arjunmehtaa/motion-capture-lite/tag_wifi.ino

#include <ESP8266WiFi.h>
#include <WiFiUdp.h>

const int NUM_LEDS = 4;
const int NUM_SEQUENCES = 5;
int ledArr[NUM_LEDS];

/* Assign pins */
const int ANALOG_PIN = A0;

/* Setup WiFi paramteres */
const char* ssid     = "dlink-A40C";
const char* password = "qybmo02053";
IPAddress local_ip(192, 168, 0, 13);                                                             
IPAddress gateway(192, 168, 0, 1);
IPAddress subnet(255, 255, 255, 0);

WiFiUDP Udp;
const char* host = "192.168.75.154";
unsigned int portToListen = 4210;  // local port to listen on
unsigned int portToSend = 5000;
char incomingPacket[2];  // buffer for incoming packets
char replyPacket[100];
unsigned long timeWindow = 10;
unsigned long readingWindow = 4;
unsigned long delayStartTime;
unsigned long delayEndTime;
unsigned long timeDelay = (timeWindow - readingWindow) / 2;
unsigned long startTime;
unsigned long currentTime;
unsigned long sequenceNumber;
bool startReading = false;
int inputVoltage = 0;

void setup() {
  Serial.begin(19200);
  pinMode(0, OUTPUT);

  // turn LED ON by default
  digitalWrite(0, LOW);
  sequenceNumber = 0;

  // We start by connecting to a WiFi network

  Serial.printf("Time window: %u, Reading window: %u\n", timeWindow, readingWindow);
  Serial.print("Connecting to ");
  Serial.println(ssid);
  
  
  WiFi.config(local_ip, gateway, subnet);
  WiFi.begin(ssid, password);
  
  while (WiFi.status() != WL_CONNECTED) {
    delay(500);
    Serial.print(".");
  }

  Serial.println("");
  Serial.println("WiFi connected");  
  // turn LED OFF when WiFi is connected
  digitalWrite(0, HIGH);
  Serial.println("IP address: ");
  Serial.println(WiFi.localIP());
  uint16 ab = Udp.begin(portToListen);
  Serial.printf("Now listening at IP %s, UDP port %d, %d\n", WiFi.localIP().toString().c_str(), portToListen, ab);

  memset(ledArr, 0, sizeof(ledArr));
}

int value = -1;

void loop() {
  currentTime = millis();
  int packetSize = Udp.parsePacket();
  if (packetSize) {

    int len = Udp.read(incomingPacket, 2);
    if (len > 0) {
      incomingPacket[len] = 0;
    }
    sequenceNumber = atoi(&incomingPacket[0]);
    // Serial.println(sequenceNumber);

    // receive incoming UDP packets
    value = 0;
    // Serial.println("Received");
    // Serial.printf("Received %d bytes from %s, port %d\n", packetSize, Udp.remoteIP().toString().c_str(), Udp.remotePort());
    startReading = true;
    startTime = currentTime;
    delayStartTime = startTime + timeDelay;
    delayEndTime = startTime + timeWindow - timeDelay;
  }
  if(startReading) {
    if(currentTime >= delayStartTime && currentTime <= delayEndTime) {
      inputVoltage = max(inputVoltage, analogRead(ANALOG_PIN)); 
    }
    if (currentTime - startTime >= timeWindow) {
      startTime = startTime + timeWindow;
      delayStartTime = startTime + timeDelay;
      delayEndTime = startTime + timeWindow - timeDelay;
      ledArr[value] = inputVoltage;
      inputVoltage = 0;
      if(value >= NUM_LEDS - 1) {
        startReading = false;
        for (int i = 0; i < NUM_LEDS; i++) {
          // strcat(replyPacket, itoa(ledArr[i], 10));
          sprintf(replyPacket, "%s%d ", replyPacket, ledArr[i]);
        }
        value = 0;
        if (sequenceNumber >= NUM_SEQUENCES - 1) {
          Udp.beginPacket(Udp.remoteIP(), portToSend);
          Udp.write(replyPacket);
          Udp.endPacket();
          memset(replyPacket, 0, sizeof(replyPacket));
        }
        memset(ledArr, 0, sizeof(ledArr));
      } else {
        value += 1;
      }
    }
  }
}
