arjunmehtaa/motion-capture-lite/udp_server.py

import socket
import time
import threading
import queue
from random import randint
import math
from typing import List

sock_listen = socket.socket(socket.AF_INET, socket.SOCK_DGRAM)

listening_udp_port = 5000
counter = 1

sock_listen.bind(("", listening_udp_port))
sock_listen.setblocking(False)

NUM_BEAMERS = 4
NUM_LEDS_PER_BEAMER = 4
NUM_TOTAL_LEDS = NUM_BEAMERS * NUM_LEDS_PER_BEAMER
NUM_TAGS = 2

from visualization import Visualization
vis = Visualization()

# prev_region = [[-1] * NUM_BEAMERS for _ in range(NUM_TAGS)]
# print(prev_region)

def get_region_number(sequence, tag_id: int, beamer_id: int):
    regions = {
    "0000": 0, "0001": 1,
    "0010": 2, "0011": 3,
    "0110": 4, "0111": 5,
    "0100": 6, "0101": 7,
    "1100": 8, "1101": 9,
    "1110": 10, "1111": 11,
    "1010": 12, "1011": 13,
    "1000": 14, "1001": 15
    }

    try:
        # print("IN: ", tag_id, beamer_id)
        # print(rnum, prev_region[tag_id][beamer_id])
        # rnum = 
        # if rnum <= 1 and prev_region[tag_id][beamer_id] >= 10:
        #     rnum = 15
        # prev_region[tag_id][beamer_id] = rnum
        return regions[sequence]
    except ValueError:
        return f"{sequence} is not a valid region"

THRESHOLD_VALUES = [
    [
        [7, 7, 12, 6], #b0
        [7, 20, 15, 6], #b1
        [7, 7, 12, 6], #b2
        [7, 20, 15, 6], #b1
    ],
    [
        [12, 30, 19, 14], #b1
        [12, 30, 19, 14], #b1
        [12, 25, 19, 14], #b2
        [12, 30, 19, 14], #b1
    ]
]

prev_four_value = [[0] * NUM_BEAMERS for _ in range(NUM_TAGS)]
prev_four_state = [["0"] * NUM_BEAMERS for _ in range(NUM_TAGS)]
def adc_to_binary(region: List[str], tag_id: int, beamer_id: int):
    """
    Converting ADC array to binary 
    (["8", "20", "8"] -> "010")
    """
    ret = ""
    for i in range(3):
        val = region[i]
        val = int(val)
        if val > THRESHOLD_VALUES[tag_id][beamer_id][i]:
            ret += "1"
        else:
            ret += "0"
    
    # 4th LED
    global prev_four_value
    global prev_four_state
    
    val4 = int(region[3])
    if val4 - prev_four_value[tag_id][beamer_id] < -1:
        ret += "0"
        prev_four_value[tag_id][beamer_id] = val4
    elif val4 - prev_four_value[tag_id][beamer_id] > 1:
        ret += "1"
        prev_four_value[tag_id][beamer_id] = val4
    else:
        ret += prev_four_state[tag_id][beamer_id]
    prev_four_state[tag_id][beamer_id] = ret[-1]

    return ret

def parse_message(message: str, tag_id: int):
    values = message.split()
    values = [int(val) for val in values]

    if len(values) != NUM_TOTAL_LEDS:
        print(f"{tag_id} did not receive {NUM_TOTAL_LEDS} values, got {len(values)} ")
        return

    try:
        beamer_values = [values[i:i + NUM_LEDS_PER_BEAMER] for i in range(0, len(values), NUM_LEDS_PER_BEAMER)]
    except Exception as e:
        print("Exception 0: ", e)

    beamer_regions = []
    print("Beamer Values:", beamer_values)
    for i in range(0, NUM_BEAMERS):
        try:
            beamer_regions.append(adc_to_binary(beamer_values[i], tag_id, i))
        except Exception as e:
            print("Exception 1: ", e, i, i + NUM_LEDS_PER_BEAMER, len(values))
    
    try:
        beamer_rnum = [get_region_number(beamer_regions[i], tag_id, i) for i in range(NUM_BEAMERS)]
    except Exception as e:
        print("Exception 2: ", e)


    #### x ####
    x_beamers = [0, 2]
    # print("x_beamers:", x_beamers)
    for i in x_beamers:
        try:
            # print(f"B{i} Threshold:     ", THRESHOLD_VALUES[tag_id][i])
            # print(f"B{i} Values:        ", beamer_values[i])
            print(f"B{i} Region Number: ", beamer_rnum[i])
        except Exception as e:
            print("adshjgsadgjhads", e)
        print()

    x = -1
    if sum(beamer_values[x_beamers[0]]) > sum(beamer_values[x_beamers[1]]):
        x = beamer_rnum[x_beamers[0]]
    else:
        x = beamer_rnum[x_beamers[1]]

    y_beamers = [3, 1]
    # print("y_beamers:", y_beamers)    
    for i in y_beamers:
        # print(f"B{i} Threshold:     ", THRESHOLD_VALUES[tag_id][i])
        # print(f"B{i} Values:        ", beamer_values[i])
        print(f"B{i} Region Number: ", beamer_rnum[i])
        print()

    # set y to whichever beamer region number has highest beamer_values
    y = -1
    # if sum(beamer_values[y_beamers[0]]) > sum(beamer_values[y_beamers[1]]):
    #     y = beamer_rnum[y_beamers[0]]
    # else:
    #     y = beamer_rnum[y_beamers[1]]
    y = beamer_rnum[y_beamers[1]] 


    z = 0
    for bvals in beamer_values:
        z += bvals[1]

    # print("z (adc):", z)
    # if z > 1000:
    #     z = math.log2(1000)
    # else:
    # print('before z division:', z)
    # print('z log:', math.log2(z), 'division', z/10)
    # z /= 10
    z = -math.log2(z) + 8

    if z < 0:
        z = 0
    if z > 2.0:
        z = 2.0
    z *= 2
    z += 4

    # print("z:", z)
    print("(x, y, z): ", x, y, z)

    # x, y = compute_xy_coordinates(180 - b1a, b2a, Point(0, 0, 0), Point(5, 0, 0))
    # print("Positions: ", b1, y)
    print()
    if tag_id == 0:
        vis.update(x, 15 - y, z, tag_id)
    elif tag_id == 1:
        vis.update(x, 15 - y, z, tag_id)
    else:
        print("tag id: ", tag_id)
        exit(1)

def receive_messages():
    counter = 0
    while True:
        try:
            data, addr = sock_listen.recvfrom(1024)
            counter += 1
            # print("Received Message:", data.decode(), "from", addr)
            print("Address:", addr)
            if (addr[0] == '192.168.0.13'):
                parse_message(data.decode(), 0)
            else:
                parse_message(data.decode(), 1)

            # message_queue.put({data, addr})
        except KeyboardInterrupt:
            print("Exiting receive_messages thread")
            sock_listen.close()
            break
        except Exception as e:
            # print(e)
            pass


if __name__ == "__main__":
    print(sock_listen.getsockname())
    receive_messages()
